Ymit24/prandtl-hardware/pictures/ray_pers_home_shadows.png

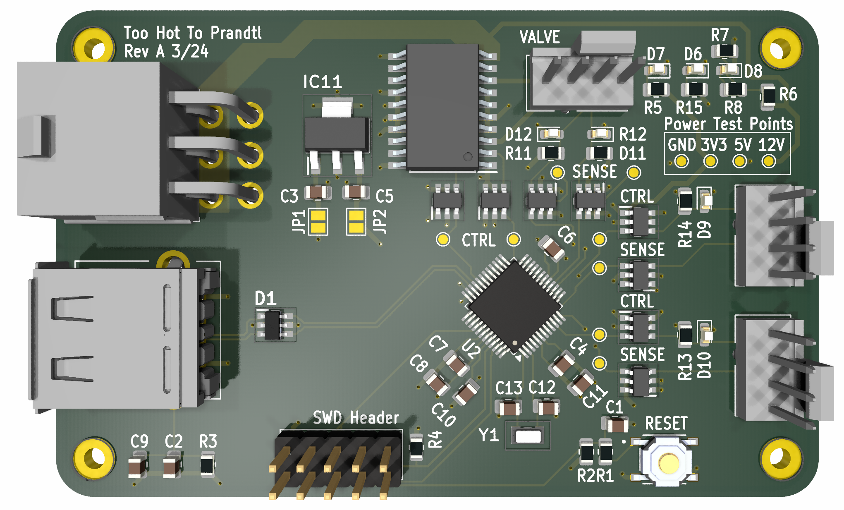
pictures/ray_pers_home_shadows.png
